pjaos/dc_load_unit/images/web6.png

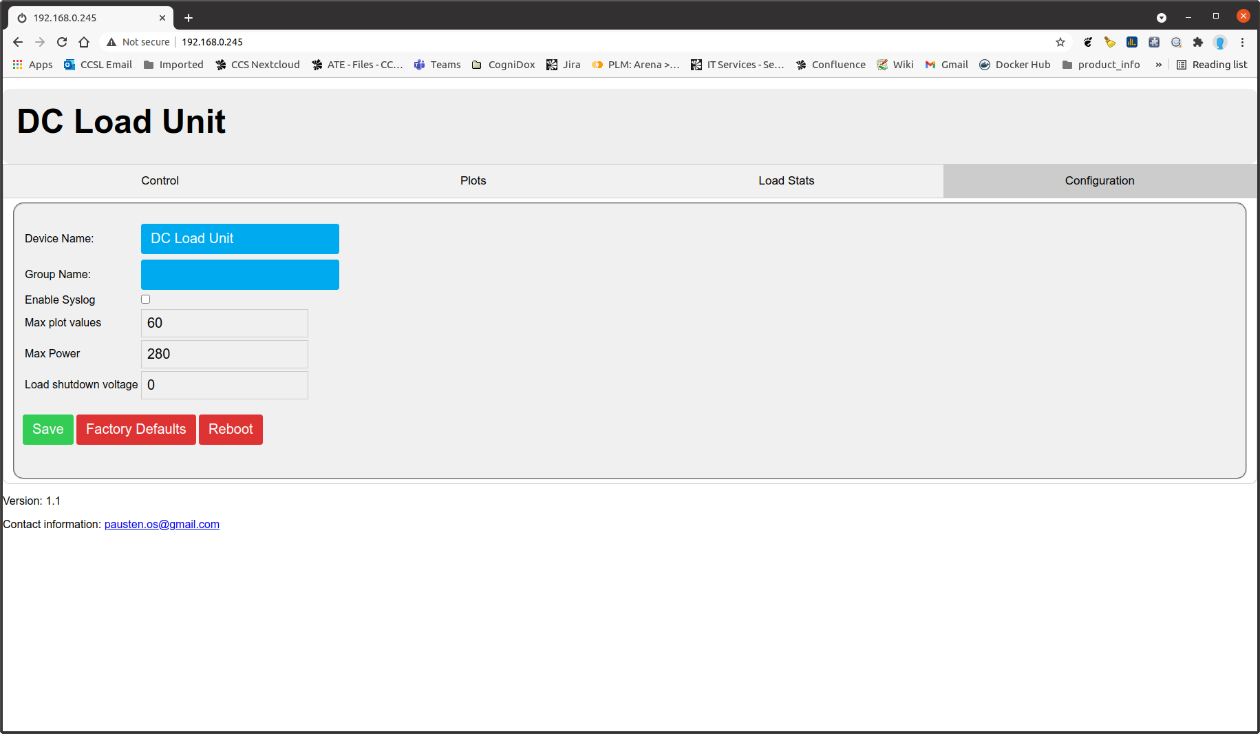
images/web6.png
