pjaos/dc_load_unit/case/cover_mk1.FCStd

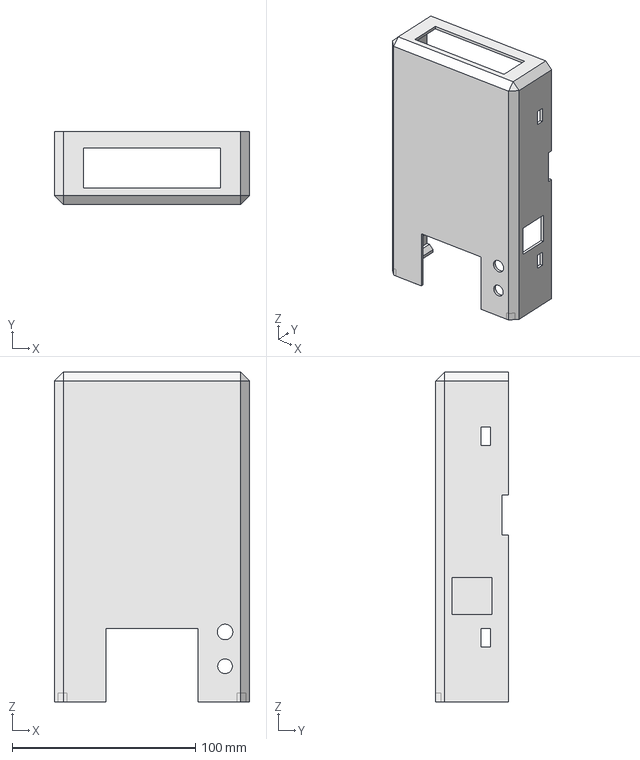
[picture p33: CAD file, 2021-05-03]
case/cover_mk1.FCStd
106.6 x 40.0 x 180.0 mm
