pjaos/dc_load_unit/case/fan_holder_wire_cover.FCStd

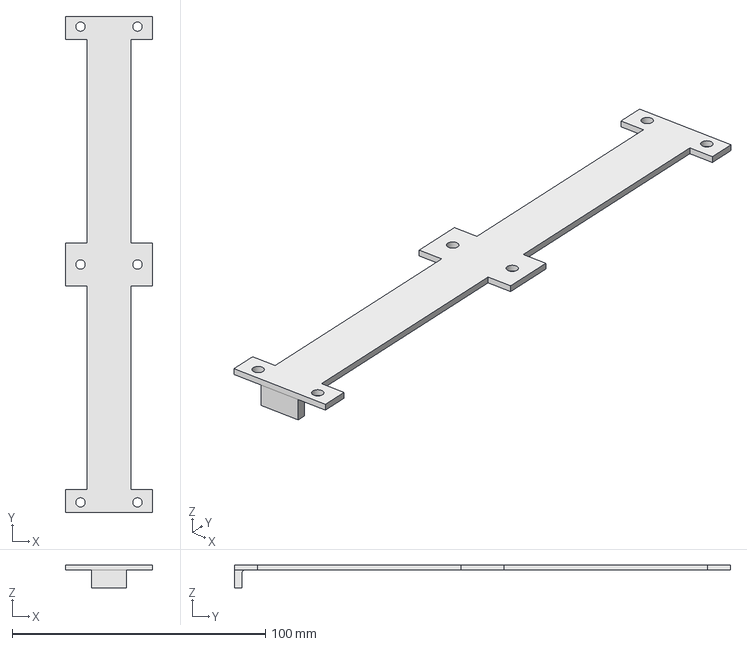
[picture p34: CAD file, 2021-05-03]
case/fan_holder_wire_cover.FCStd
34.5 x 196.0 x 9.00 mm
