pjaos/dc_load_unit/case/front_foot_mk2.FCStd

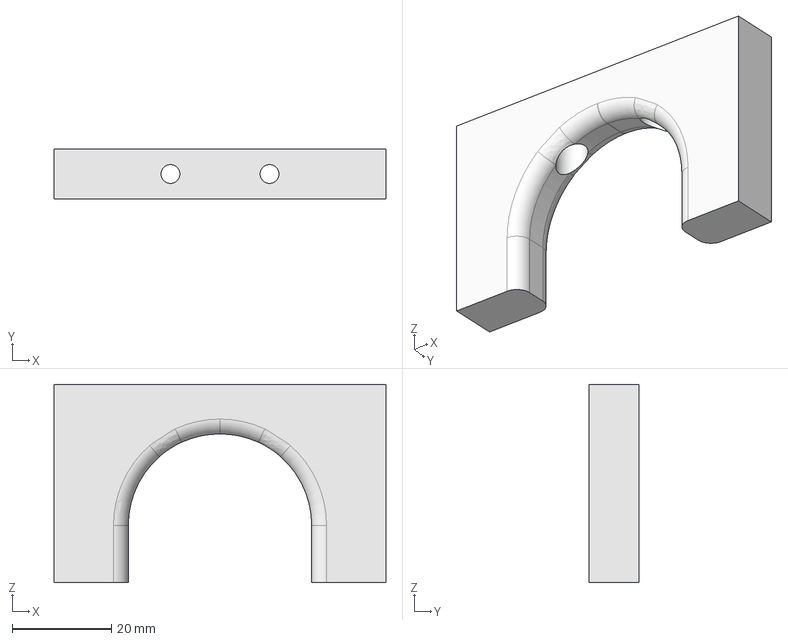
[picture p35: CAD file, 2021-05-03]
case/front_foot_mk2.FCStd
67.0 x 10.0 x 40.0 mm
