pjaos/dc_load_unit/case/top_grill_mk1.FCStd

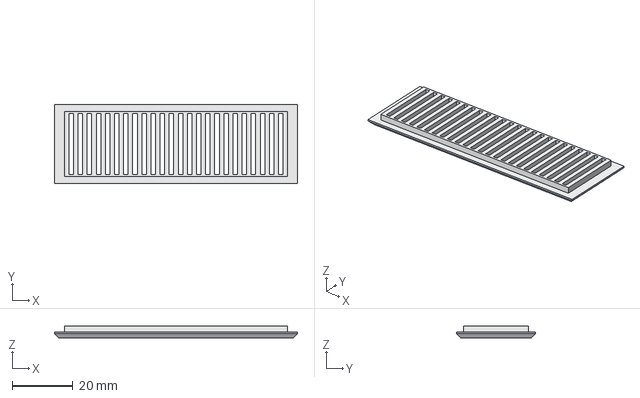
[picture p36: CAD file, 2021-05-03]
case/top_grill_mk1.FCStd
80.0 x 26.0 x 4.00 mm
