pjaos/dc_load_unit/case/fan_holder_clip_mk1.FCStd

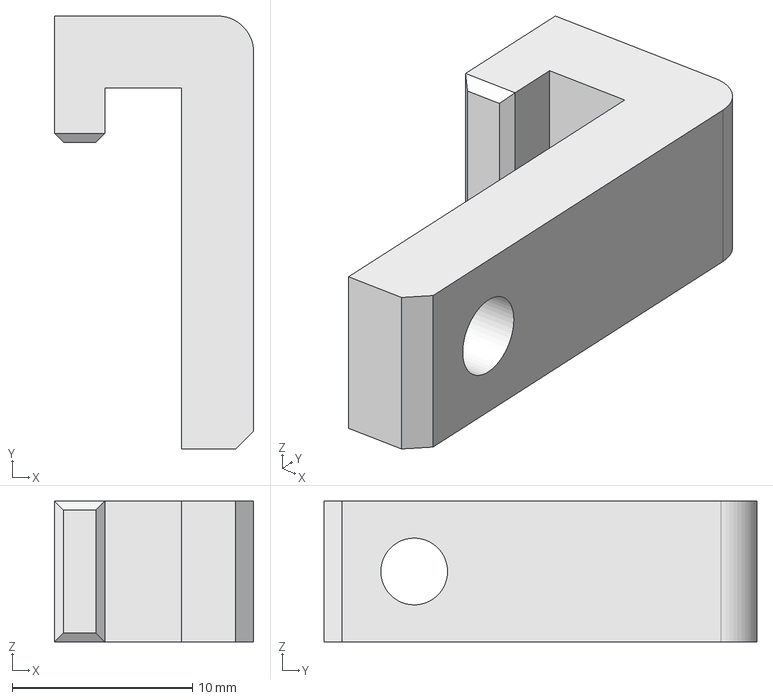
[picture p37: CAD file, 2021-05-03]
case/fan_holder_clip_mk1.FCStd
11.1 x 24.0 x 7.80 mm
