pjaos/dc_load_unit/case/insert_test_part_mk2.FCStd

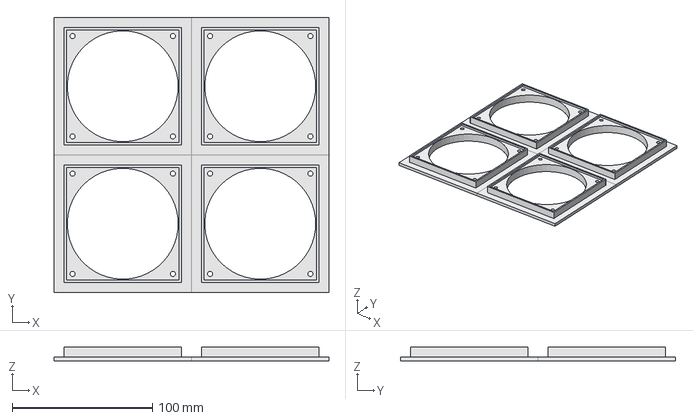
[picture p38: CAD file, 2021-05-03]
case/insert_test_part_mk2.FCStd
196.0 x 196.0 x 10.0 mm
