pjaos/dc_load_unit/case/cover_bracket.FCStd

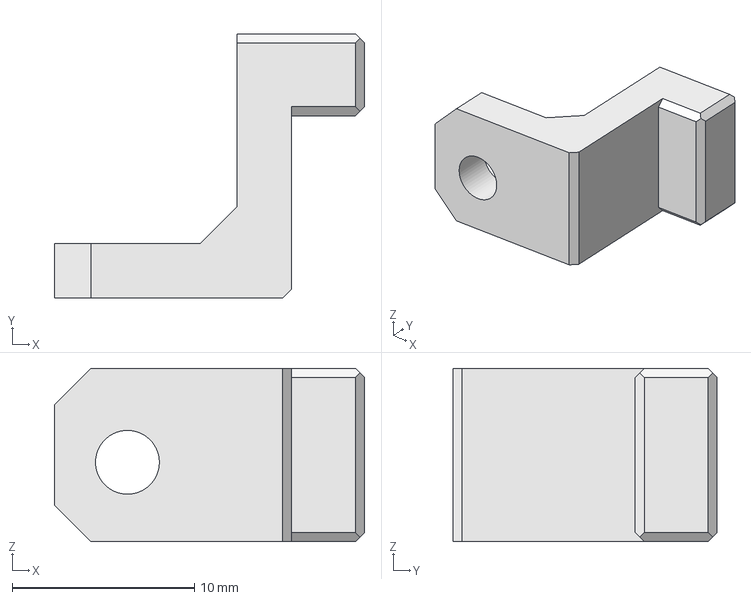
[picture p39: CAD file, 2021-05-03]
case/cover_bracket.FCStd
17.0 x 14.5 x 9.50 mm
