pjaos/dc_load_unit/case/side_block.FCStd

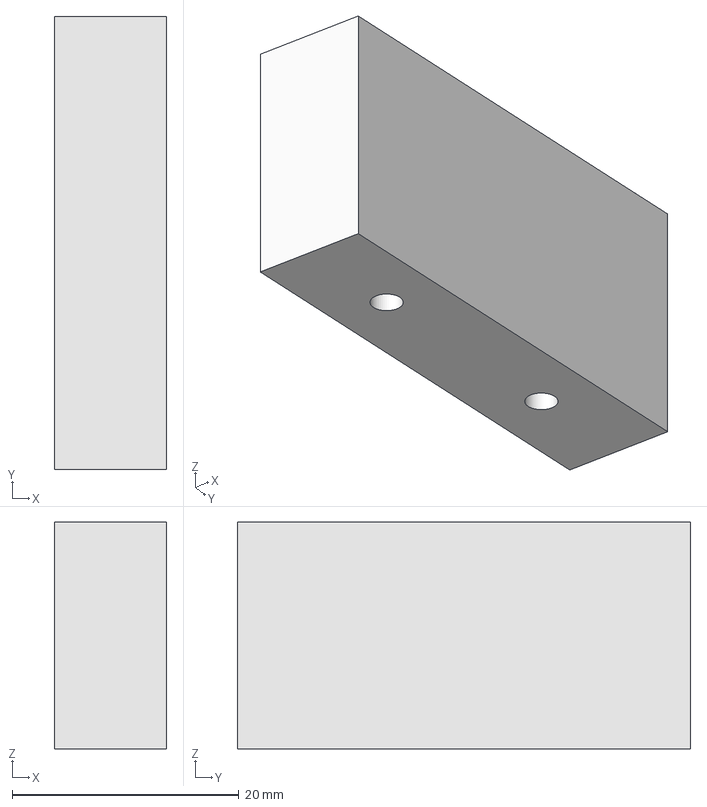
[picture p40: CAD file, 2021-05-03]
case/side_block.FCStd
9.90 x 40.0 x 20.0 mm
