pjaos/dc_load_unit/case/spacer.FCStd

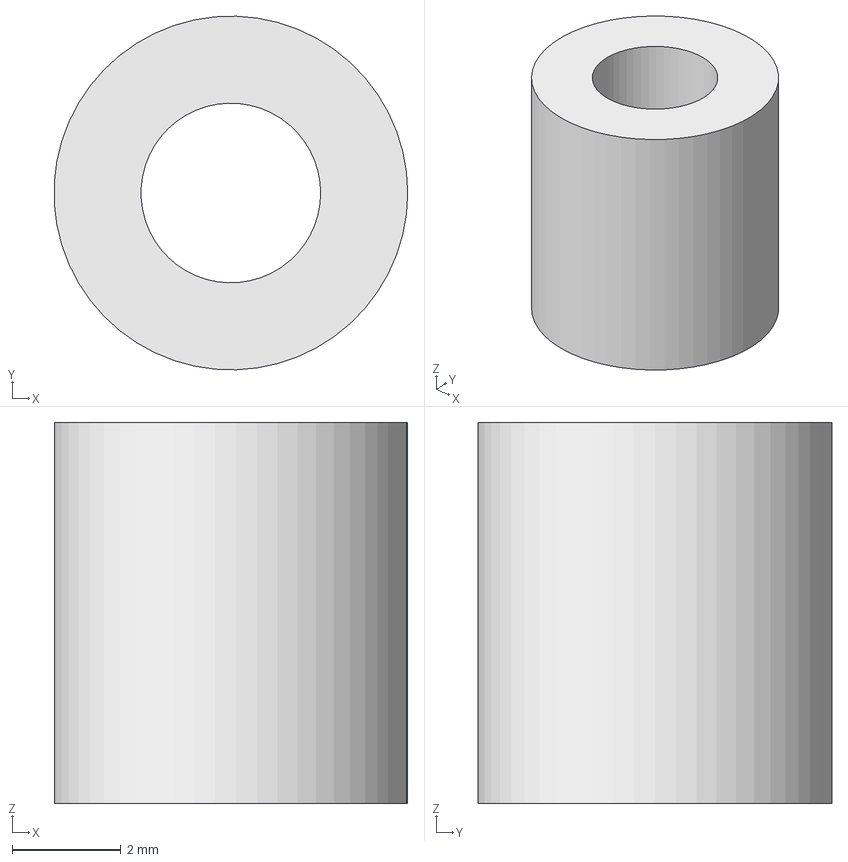
[picture p41: CAD file, 2021-05-03]
case/spacer.FCStd
6.49 x 6.50 x 7.00 mm
