pjaos/dc_load_unit/case/rear_foot.FCStd

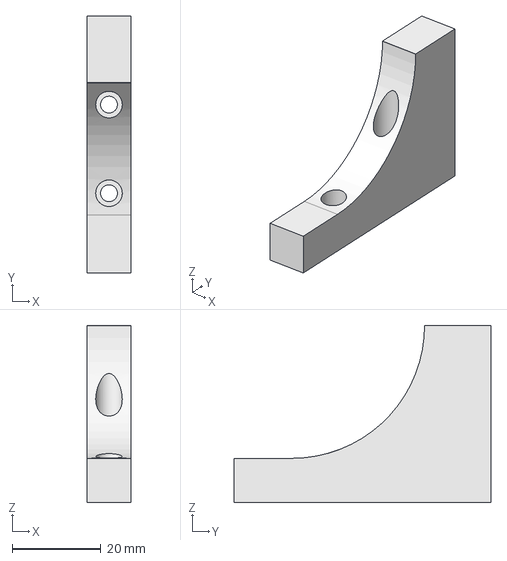
[picture p42: CAD file, 2021-05-03]
case/rear_foot.FCStd
9.90 x 58.0 x 40.0 mm
