pjaos/dc_load_unit/software/src/fan.c

#include <mgos.h>
#include <mgos_gpio.h>

#include "log.h"
#include "fan.h"

#define FAN1_GPIO 27
#define FAN2_GPIO 26
#define FAN3_GPIO 25
#define FAN4_GPIO 33
#define FAN5_GPIO 32

#define FAN1_THRESHOLD_TEMP 50
#define FAN2_THRESHOLD_TEMP 55
#define FAN3_THRESHOLD_TEMP 55
#define FAN4_THRESHOLD_TEMP 55
#define FAN5_THRESHOLD_TEMP 55
#define FAN_TEMP_HYSTERESIS  1

static uint8_t fan_state_array[5] = {0,0,0,0,0};
static uint8_t fan_on_count;

enum fan_id_list{FAN1=1, FAN2, FAN3, FAN4, FAN5};

extern char syslog_msg_buf[SYSLOG_MSG_BUF_SIZE];

/**
 * @brief Get the number of cooling fans currently switch on.
 * @return The number of active fans.
 */
uint8_t get_fan_on_count(void) {
    return fan_on_count;
}

/**
 * @brief Set the fan on/off state.
 * @param fan ID The ID of the fan to be set.
 * @return void.
 */
void set_fan_state(uint8_t fan_id, bool on) {
    if( fan_id == FAN1 ) {
        mgos_gpio_write(FAN1_GPIO, on);
    }
    else if( fan_id == FAN2 ) {
        mgos_gpio_write(FAN2_GPIO, on);
    }
    else if( fan_id == FAN3 ) {
        mgos_gpio_write(FAN3_GPIO, on);
    }
    else if( fan_id == FAN4 ) {
        mgos_gpio_write(FAN4_GPIO, on);
    }
    else if( fan_id == FAN5 ) {
        mgos_gpio_write(FAN5_GPIO, on);
    }
    snprintf(syslog_msg_buf, SYSLOG_MSG_BUF_SIZE, "%s: FAN: %d, state: %d", __FUNCTION__, fan_id, on);
    log_msg(LL_DEBUG, syslog_msg_buf);

}

/**
 * @brief Set a fan on/off.
 * @param fan_id The fan identifier number.
 * @param temp The heat sink temperature.
 * @return true if the fan is set on..
 */
static void update_fan_state(uint8_t fan_id, float temp) {
    float threshold_temp = 0.0;

    if( fan_id == FAN1 ) {
        threshold_temp = FAN1_THRESHOLD_TEMP;
    }
    else if( fan_id == FAN2 ) {
        threshold_temp = FAN2_THRESHOLD_TEMP;
    }
    else if( fan_id == FAN3 ) {
        threshold_temp = FAN3_THRESHOLD_TEMP;
    }
    else if( fan_id == FAN4 ) {
        threshold_temp = FAN4_THRESHOLD_TEMP;
    }
    else if( fan_id == FAN5 ) {
        threshold_temp = FAN5_THRESHOLD_TEMP;
    }

    //Turn on the fan if required
    if( temp >=  threshold_temp ) {
        set_fan_state(fan_id, true);
        fan_state_array[fan_id-1]=1;
    }

    //Turn fan off if required
    if( temp <= threshold_temp-FAN_TEMP_HYSTERESIS ) {
        set_fan_state(fan_id, false);
        fan_state_array[fan_id-1]=0;
    }

}

void set_cooling(float temp) {
    int fanID;
    uint8_t active_fan_count = 0;

    for( fanID = FAN1 ; fanID <= FAN5 ; fanID++ ) {
        update_fan_state(fanID, temp);
        if( fan_state_array[fanID-1] ) {
            active_fan_count++;
        }
    }
    fan_on_count = active_fan_count;
}

/**
 * @Init all the fan outputs and turn off fans.
 */
void init_fans(void) {
    mgos_gpio_set_mode(FAN1_GPIO, MGOS_GPIO_MODE_OUTPUT);
    mgos_gpio_set_mode(FAN2_GPIO, MGOS_GPIO_MODE_OUTPUT);
    mgos_gpio_set_mode(FAN3_GPIO, MGOS_GPIO_MODE_OUTPUT);
    mgos_gpio_set_mode(FAN4_GPIO, MGOS_GPIO_MODE_OUTPUT);
    mgos_gpio_set_mode(FAN5_GPIO, MGOS_GPIO_MODE_OUTPUT);

    mgos_gpio_write(FAN1_GPIO, false);
    mgos_gpio_write(FAN2_GPIO, false);
    mgos_gpio_write(FAN3_GPIO, false);
    mgos_gpio_write(FAN4_GPIO, false);
    mgos_gpio_write(FAN5_GPIO, false);

}
